roboticsuic/UIC-Easy-Breath/3D files/V6.SLDPRT

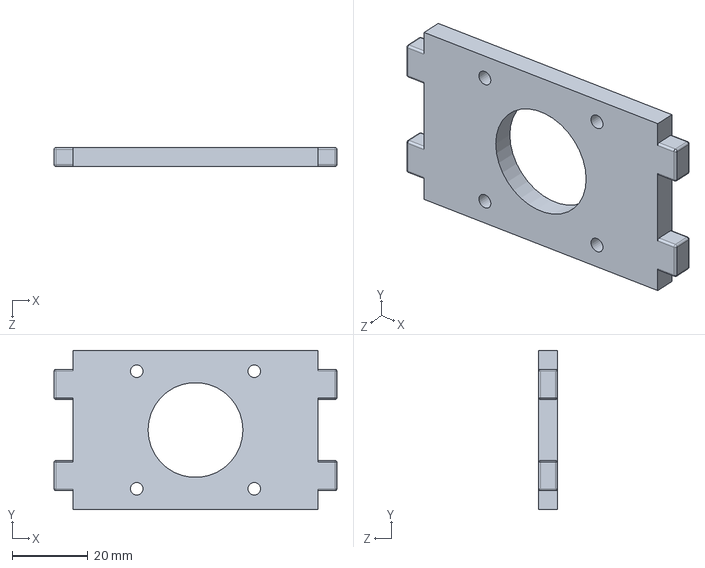
[picture p32: CAD file, 2021-02-04, an earlier design]
3D files/V6.SLDPRT
74.6 x 42.0 x 5.00 mm
