roboticsuic/UIC-Easy-Breath/3D files/V5.SLDPRT

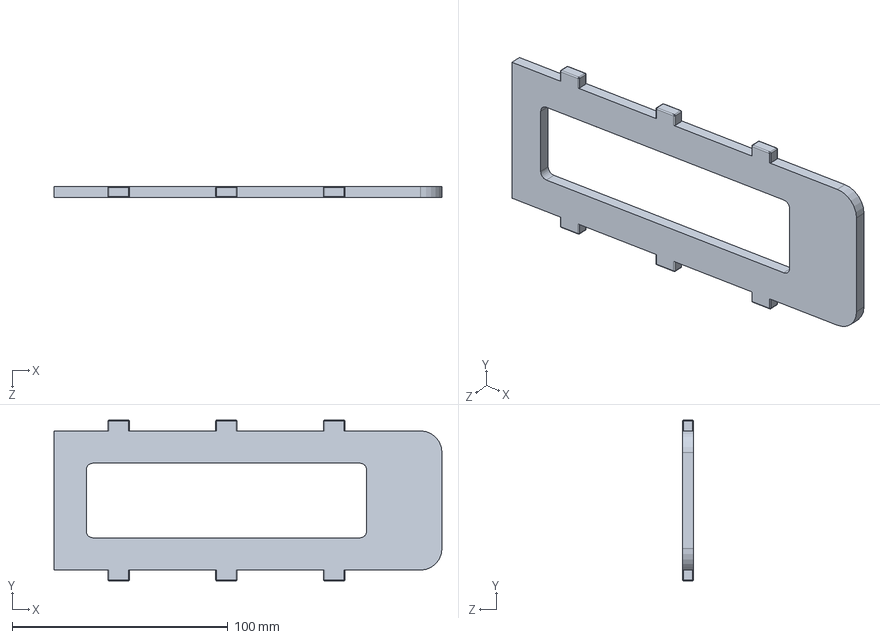
[picture p33: CAD file, 2021-02-04, an earlier design]
3D files/V5.SLDPRT
180.0 x 74.6 x 5.00 mm
