roboticsuic/UIC-Easy-Breath/3D files/V8.SLDPRT

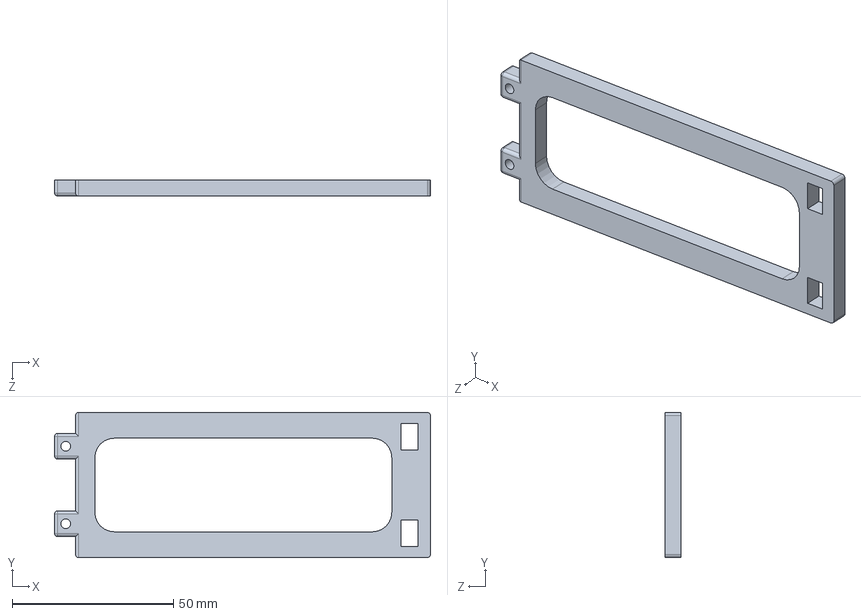
[picture p34: CAD file, 2021-02-04, an earlier design]
3D files/V8.SLDPRT
116.5 x 45.0 x 5.00 mm
